RBEGamer/SimpleArduinoBinaryClock/BILDER/Foto 05.11.14 07 58 21.jpg

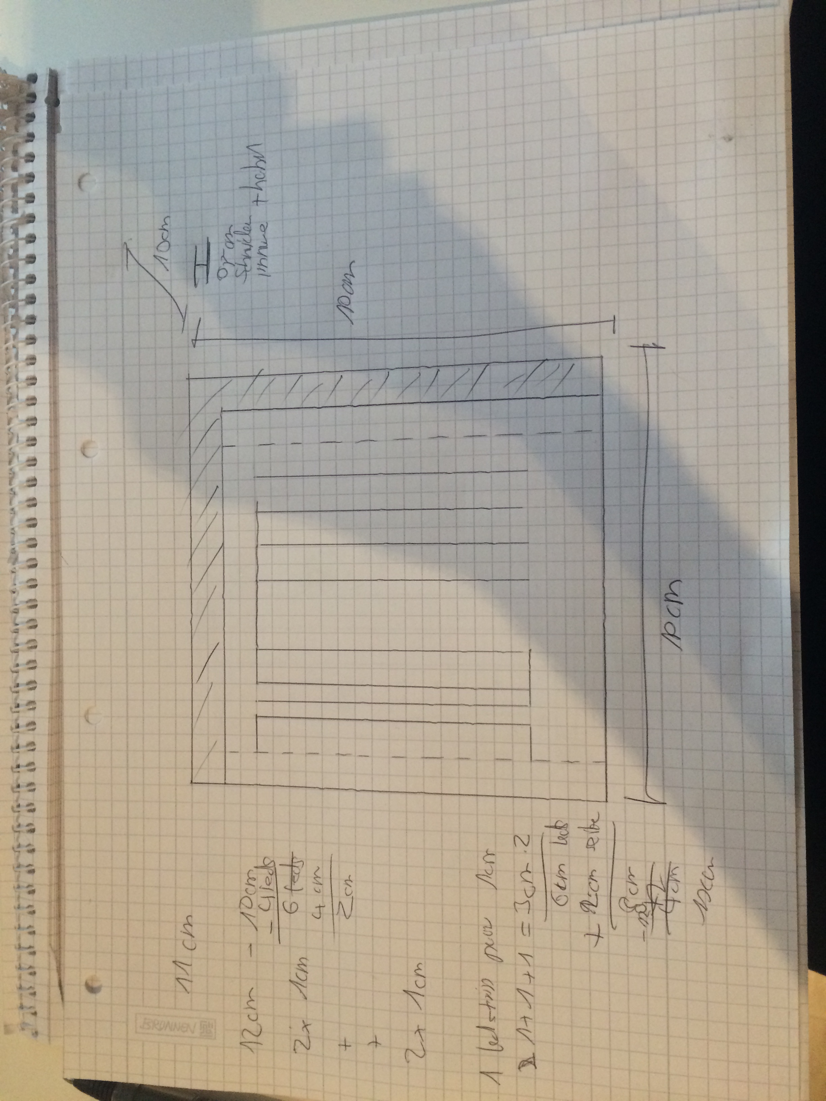
BILDER/Foto 05.11.14 07 58 21.jpg
