RBEGamer/SimpleArduinoBinaryClock/BILDER/Foto 05.11.14 07 58 25.jpg

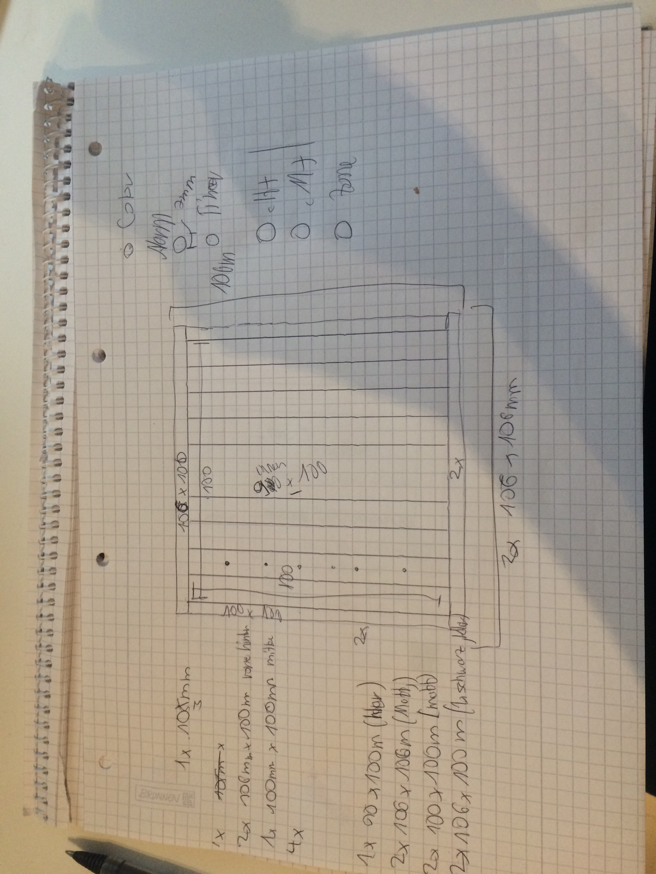
BILDER/Foto 05.11.14 07 58 25.jpg
