RBEGamer/SimpleArduinoBinaryClock/BILDER/Foto 05.11.14 21 40 19.jpg

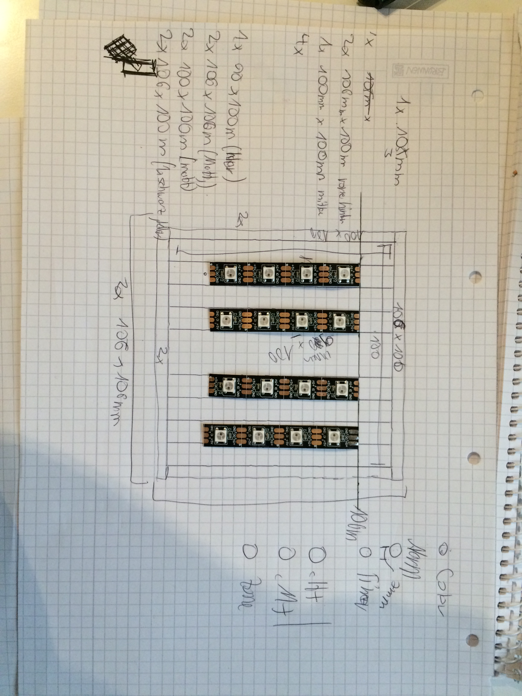
BILDER/Foto 05.11.14 21 40 19.jpg
