RBEGamer/SimpleArduinoBinaryClock/BILDER/Foto 05.11.14 22 30 46.jpg

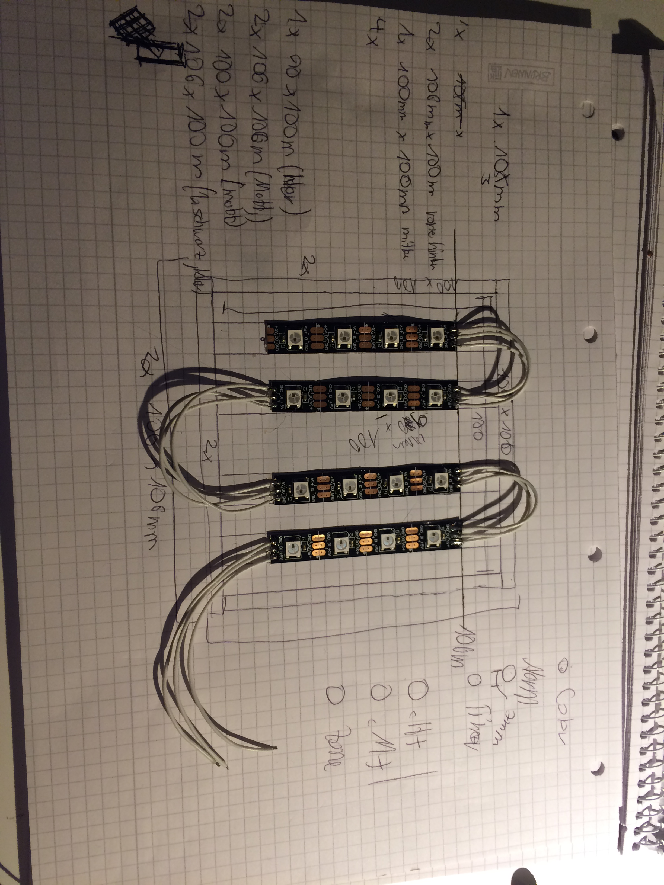
BILDER/Foto 05.11.14 22 30 46.jpg
