RBEGamer/SimpleArduinoBinaryClock/BILDER/Foto 10.11.14 14 25 55.jpg

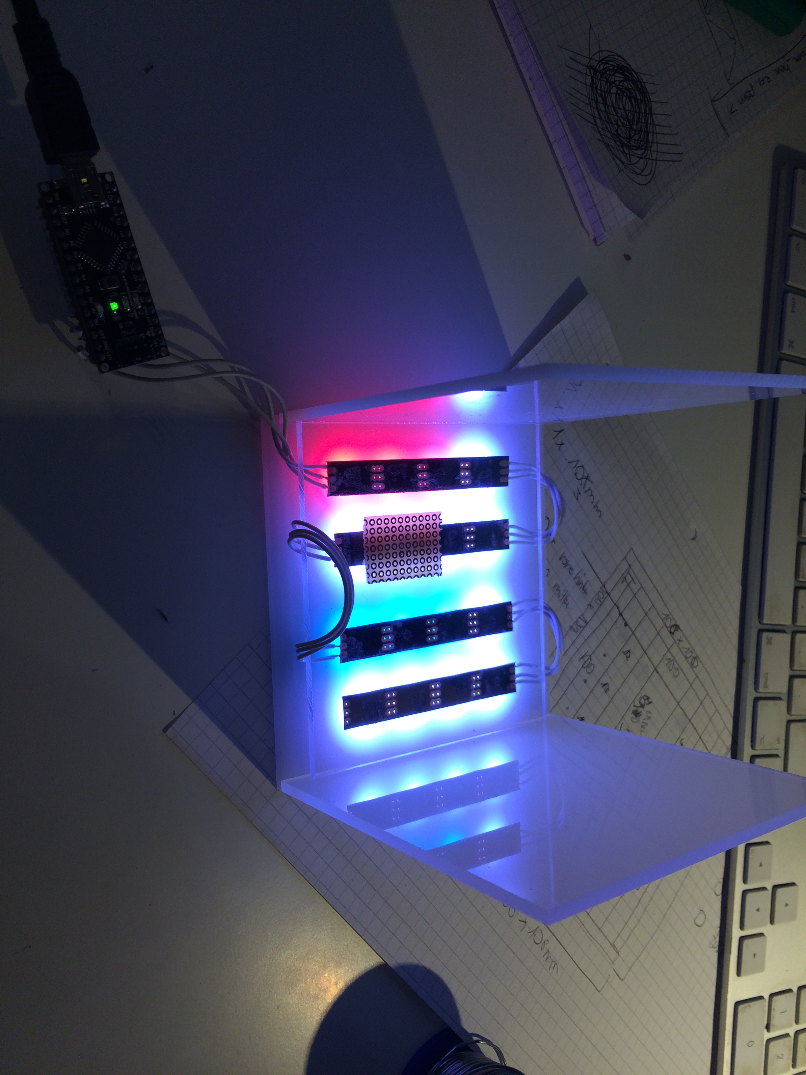
BILDER/Foto 10.11.14 14 25 55.jpg
