RBEGamer/SimpleArduinoBinaryClock/BILDER/Foto 10.11.14 20 23 38.jpg

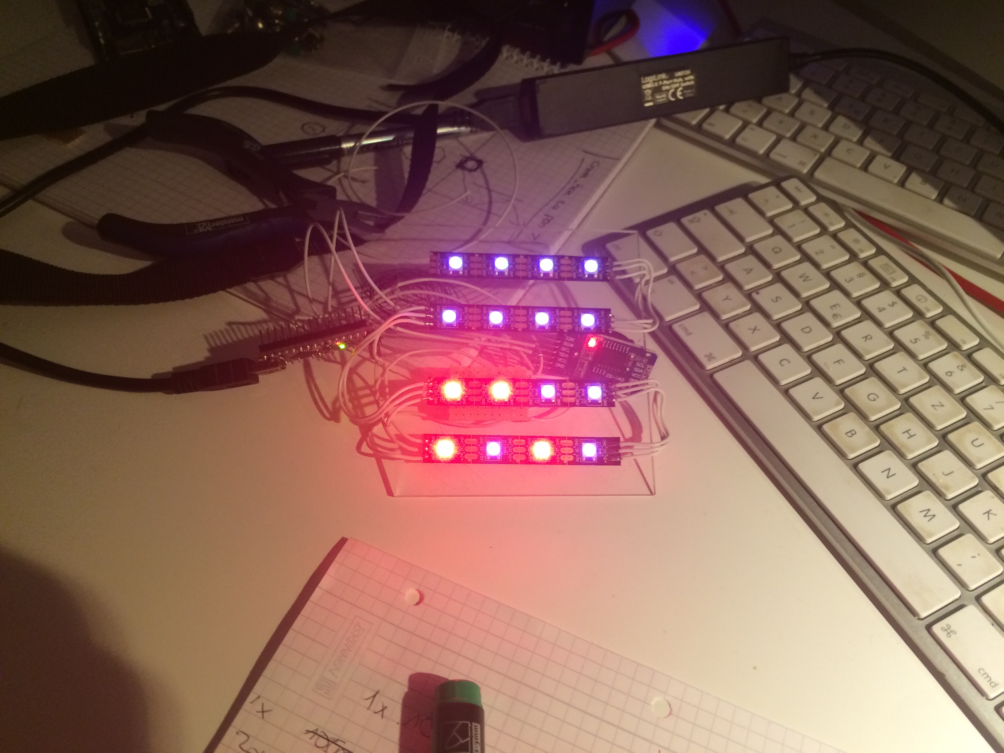
BILDER/Foto 10.11.14 20 23 38.jpg
