RBEGamer/SimpleArduinoBinaryClock/BILDER/Foto 11.11.14 00 30 37.jpg

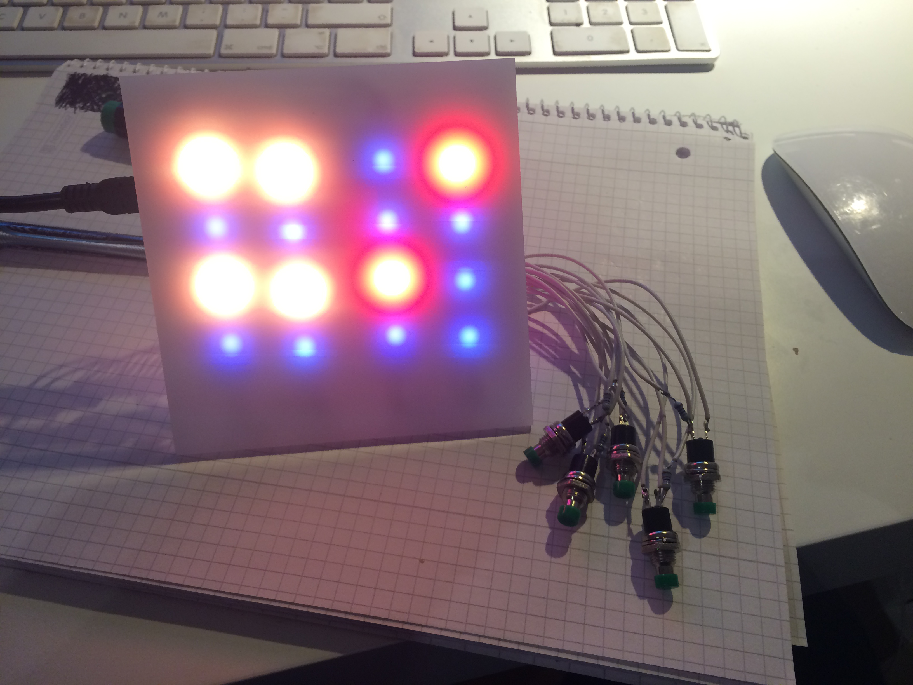
BILDER/Foto 11.11.14 00 30 37.jpg
