RBEGamer/SimpleArduinoBinaryClock/BILDER/Foto 12.11.14 22 25 32 (2).jpg

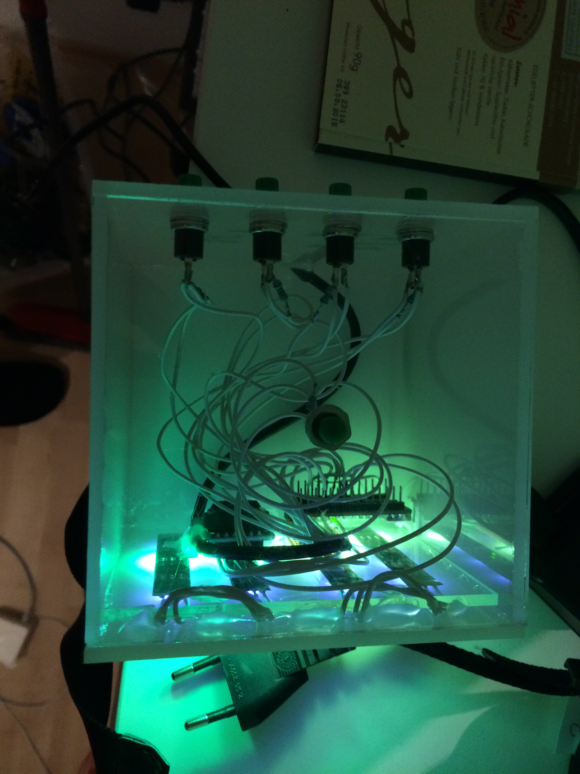
BILDER/Foto 12.11.14 22 25 32 (2).jpg
