RBEGamer/SimpleArduinoBinaryClock/src/bin_clock_eagle/bla.png

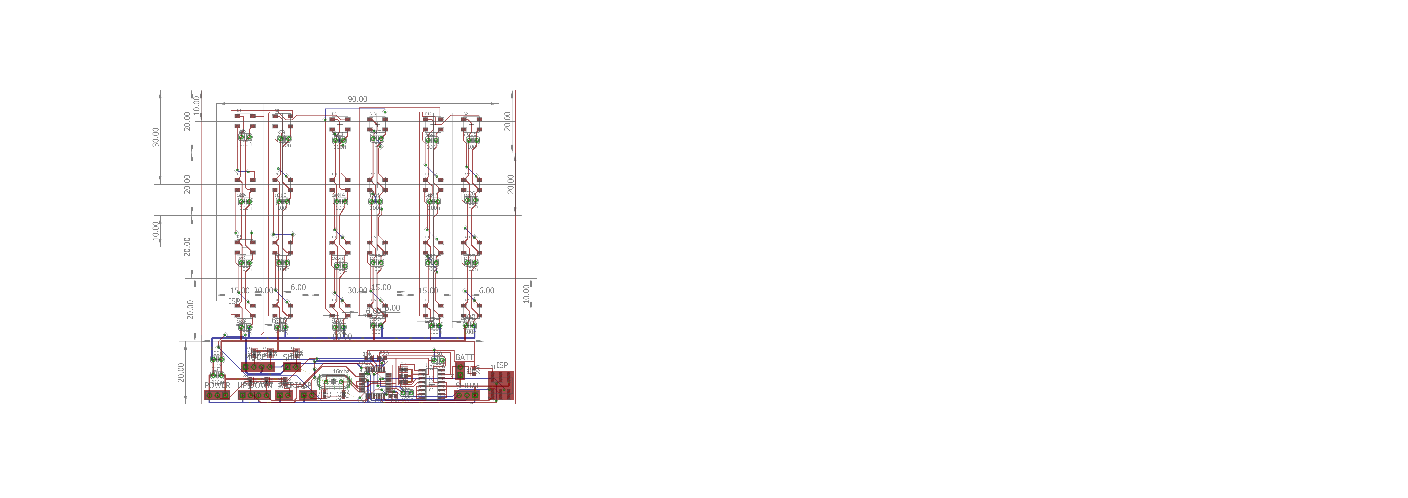
src/bin_clock_eagle/bla.png
